qookei/paaliaq/rtl/font.py

import itertools

# This font has been obtained from here:
# https://github.com/viler-int10h/vga-text-mode-fonts
# It is the is SYSTEM/FREEBSD/CP437_T.F16 font.

_font_bitmap = [
    # U+0000 NUL
    "                ",
    "                ",
    "                ",
    "                ",
    "                ",
    "                ",
    "                ",
    "                ",
    "                ",
    "                ",
    "                ",
    "                ",
    "                ",
    "                ",
    "                ",
    "                ",
    # U+263a WHITE SMILING FACE
    "                ",
    "                ",
    "  ############  ",
    "##            ##",
    "##  ##    ##  ##",
    "##            ##",
    "##            ##",
    "##  ########  ##",
    "##    ####    ##",
    "##            ##",
    "##            ##",
    "  ############  ",
    "                ",
    "                ",
    "                ",
    "                ",
    # U+263b BLACK SMILING FACE
    "                ",
    "                ",
    "  ############  ",
    "################",
    "####  ####  ####",
    "################",
    "################",
    "####        ####",
    "######    ######",
    "################",
    "################",
    "  ############  ",
    "                ",
    "                ",
    "                ",
    "                ",
    # U+2665 BLACK HEART SUIT
    "                ",
    "                ",
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
    "                ",
    "                ",
    "                ",
    "                ",
    "                ",
    # U+00a0 NO-BREAK SPACE
    "                ",
    "                ",
    "                ",
    "                ",
    "                ",
    "                ",
    "                ",
    "                ",
    "                ",
    "                ",
    "                ",
    "                ",
    "                ",
    "                ",
    "                ",
    "                ",
]

def get_font_data():
    def _str_to_byte(line):
        o = 0
        for i, v in enumerate(itertools.batched(line, 2)):
            v = 1 if v == ("#", "#") else 0
            o |= v << (7 - i)
        return o

    return [_str_to_byte(x) for x in _font_bitmap]
